cmayor314/Fishinator005/Supervisor/screencaps/ui_Fishinator Services.png

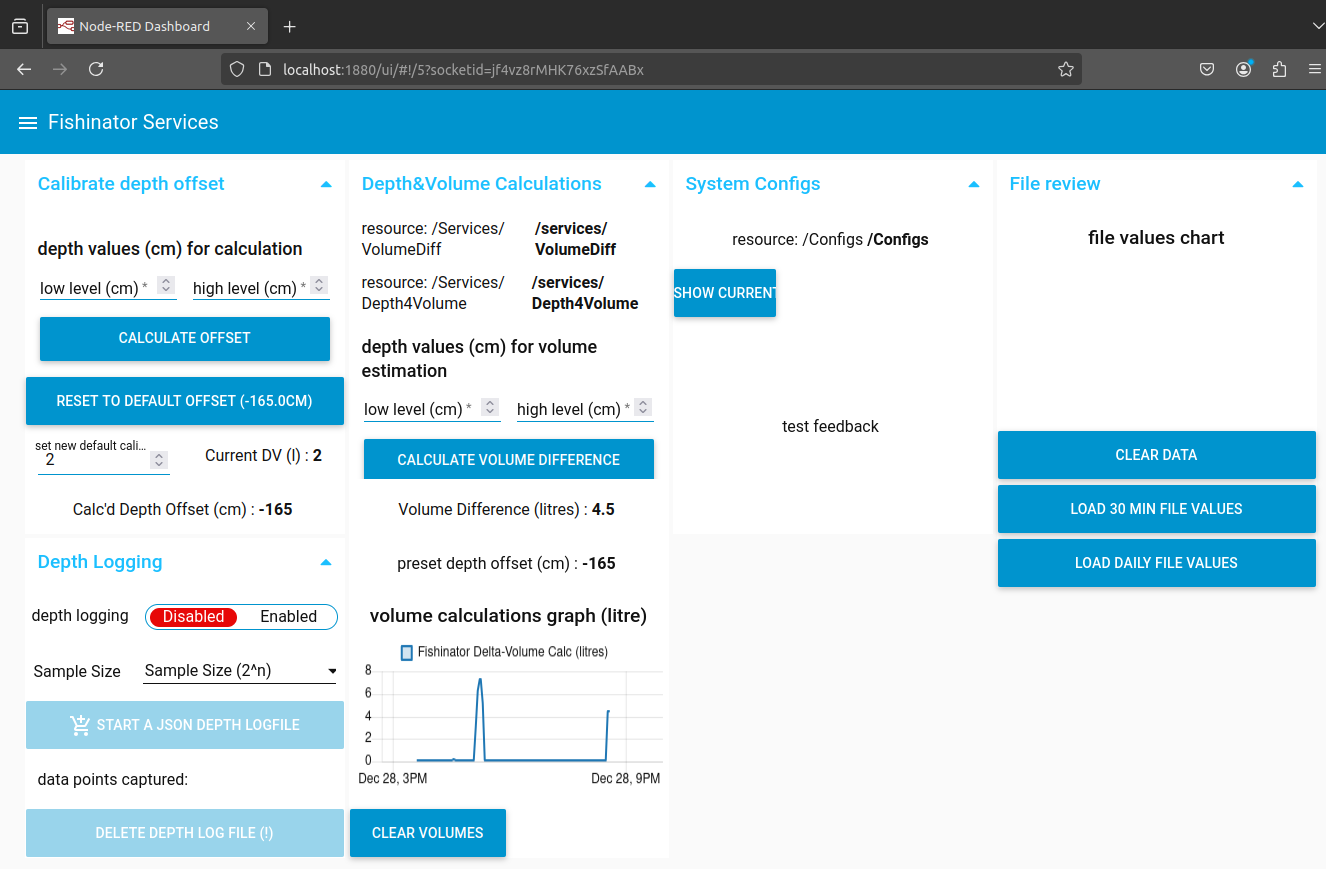
Supervisor/screencaps/ui_Fishinator Services.png
